mrWheel/DSMRlogger2HTTP/DSMR3Dbox/3D_Kastje GtM_b.JPG

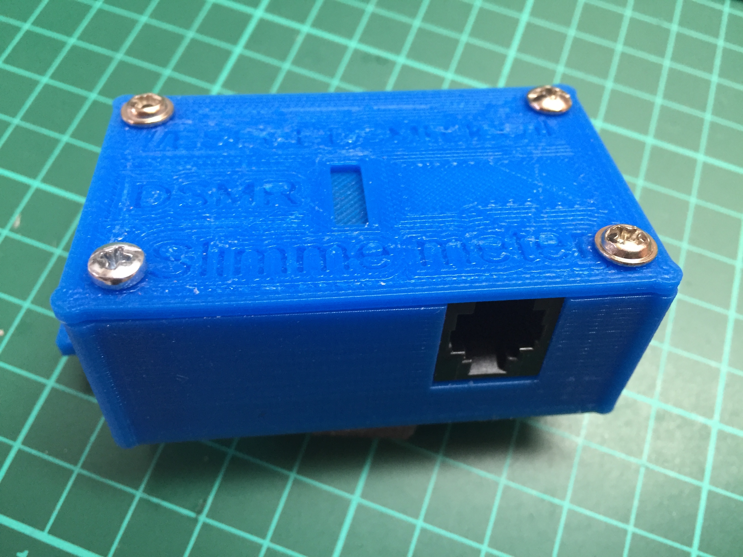
DSMR3Dbox/3D_Kastje GtM_b.JPG
