mrWheel/DSMRlogger2HTTP/DSMR3Dbox/3D_Kastje_GtM_a.JPG

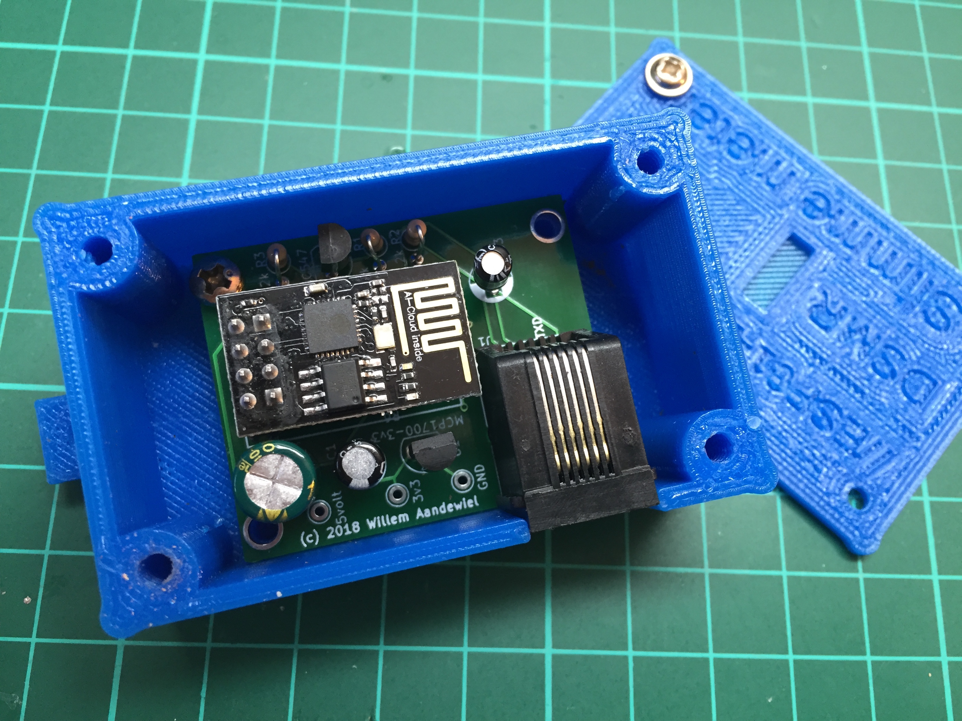
DSMR3Dbox/3D_Kastje_GtM_a.JPG
