mrWheel/DSMRlogger2HTTP/DSMR3Dbox/3D_Kastje_GtM_c.JPG

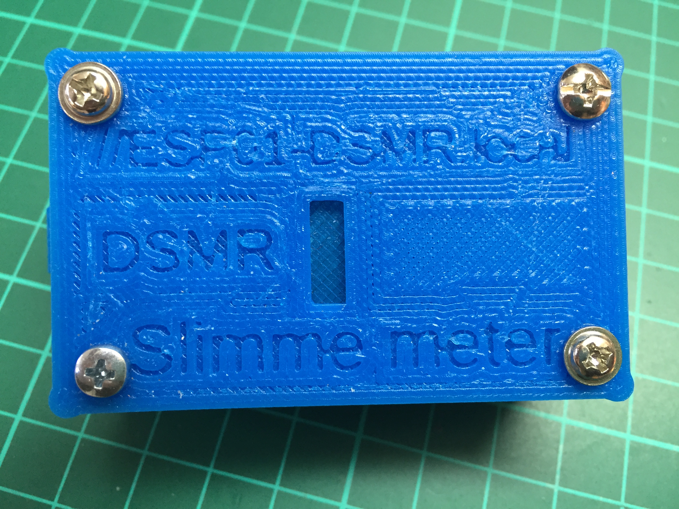
DSMR3Dbox/3D_Kastje_GtM_c.JPG
