mrWheel/DSMRlogger2HTTP/images/BB_Side-1.jpg

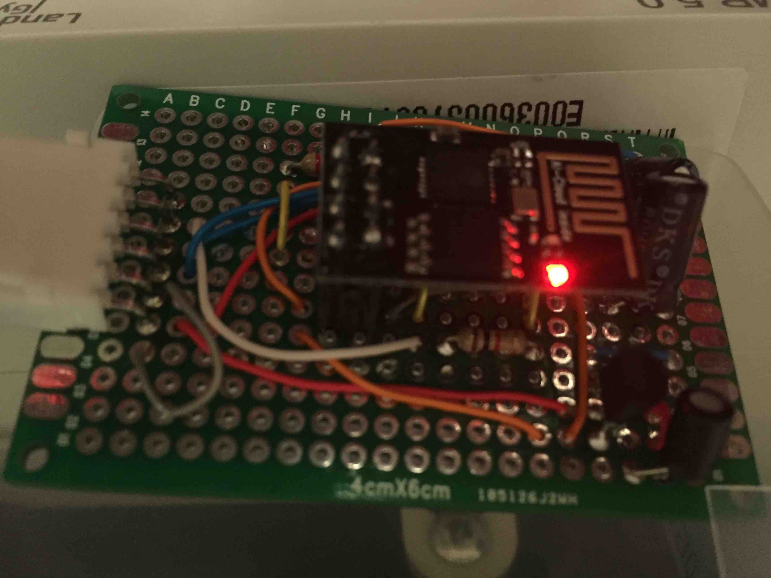
images/BB_Side-1.jpg
