mrWheel/DSMRlogger2HTTP/images/DSMR_7_Dagen.png

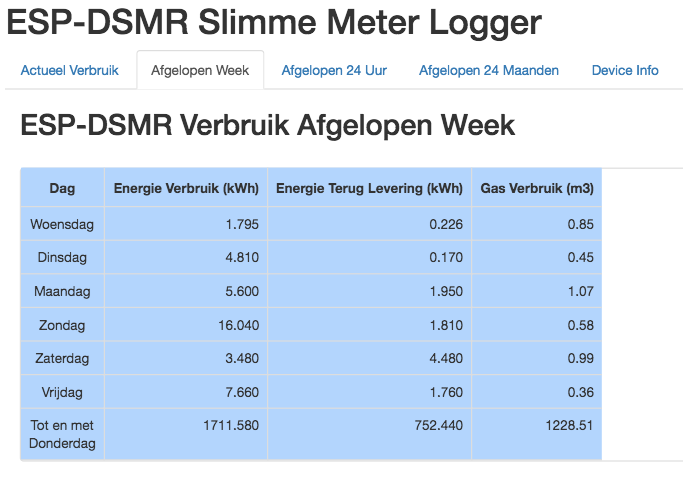
images/DSMR_7_Dagen.png
