mrWheel/DSMRlogger2HTTP/images/DSMR_24_Maanden.png

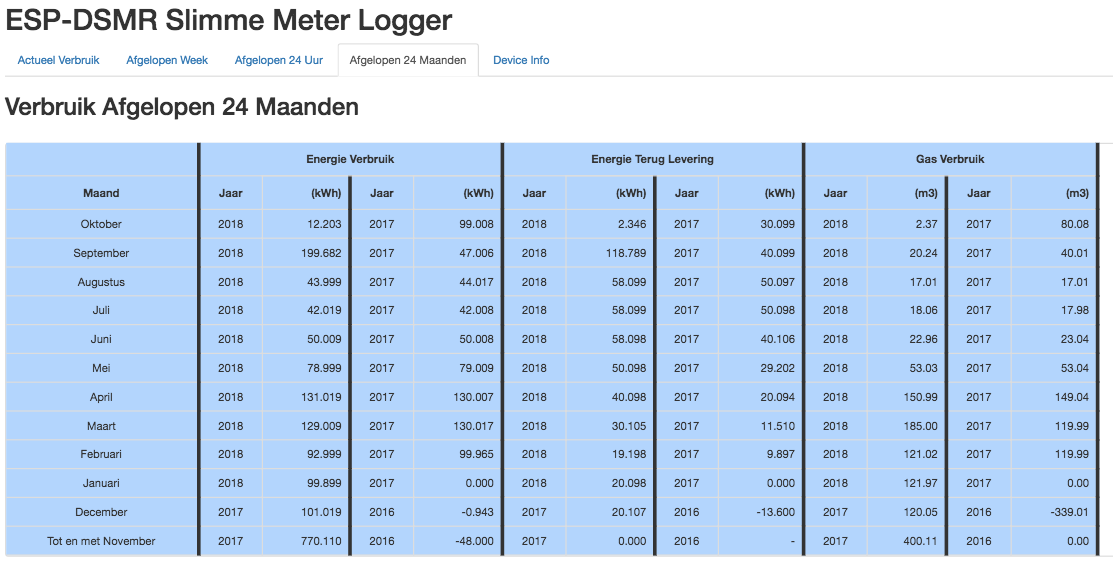
images/DSMR_24_Maanden.png
