mrWheel/DSMRlogger2HTTP/images/DSMR_24_Uur.png

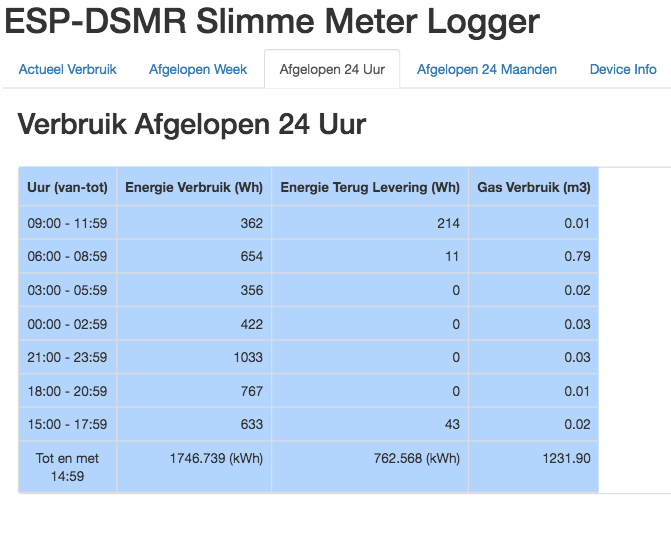
images/DSMR_24_Uur.png
