mrWheel/DSMRlogger2HTTP/images/KiCAD PCBnew.png

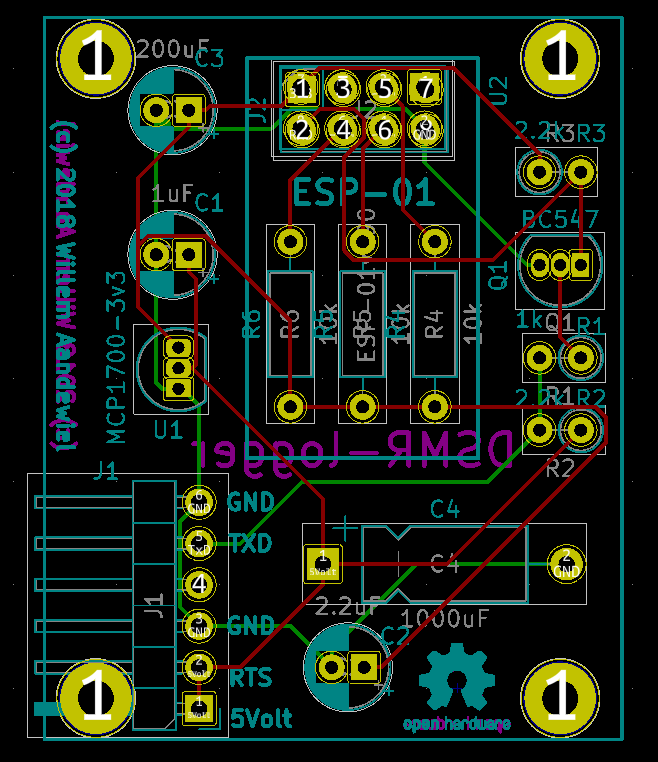
images/KiCAD PCBnew.png
