mrWheel/DSMRlogger2HTTP/mkdocs/docs/img/DSMR Last Week.png

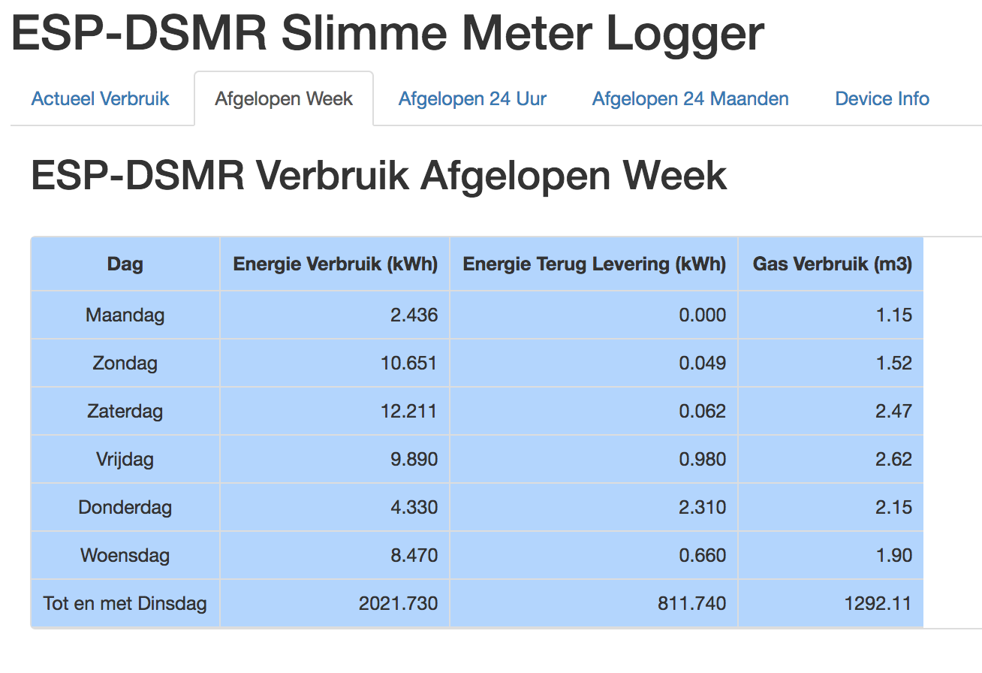
mkdocs/docs/img/DSMR Last Week.png
