mrWheel/DSMRlogger2HTTP/mkdocs/docs/img/DSMR_Top2_v3.png

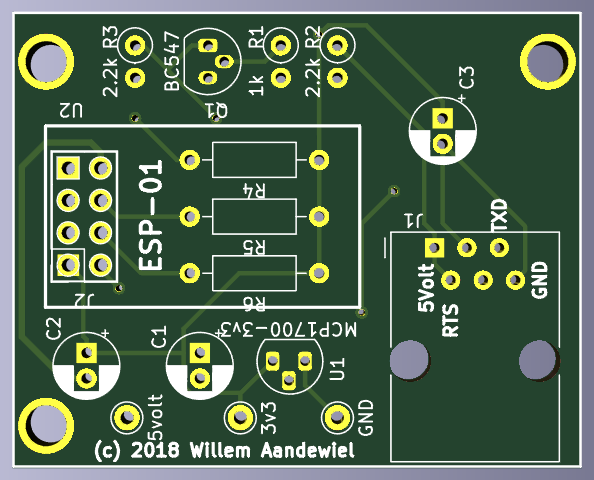
mkdocs/docs/img/DSMR_Top2_v3.png
