mrWheel/DSMRlogger2HTTP/mkdocs/docs/img/DSMRweek.png

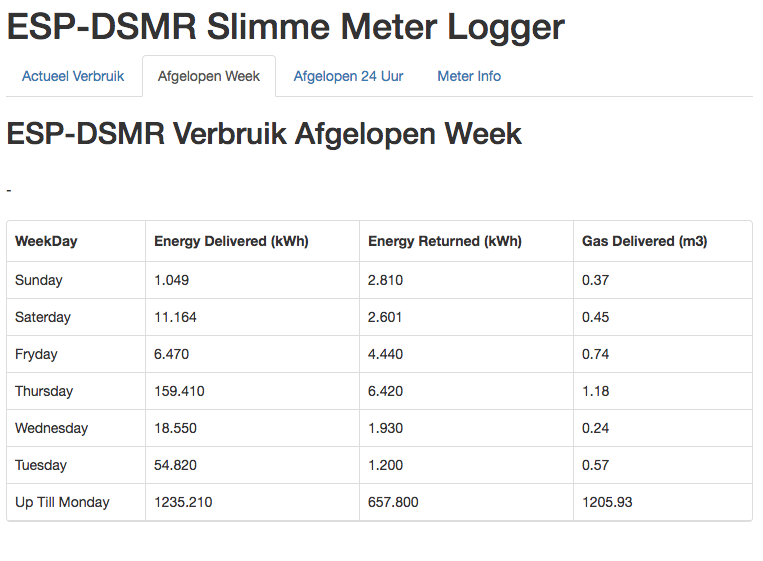
mkdocs/docs/img/DSMRweek.png
